2ME3Elektronika/25-26_AudioScope/Material/Fun Generation UA-202.png

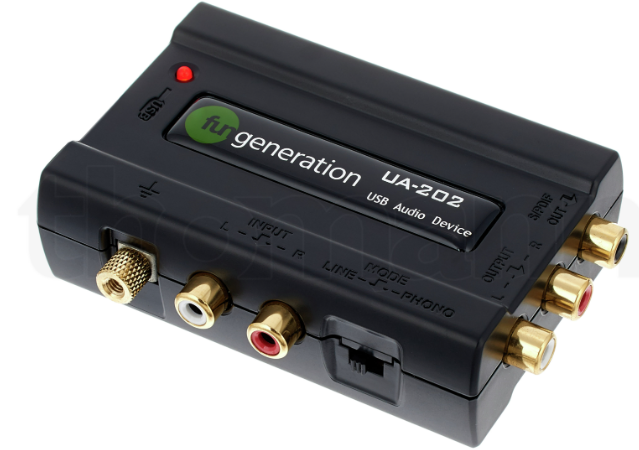
Material/Fun Generation UA-202.png
