2ME3Elektronika/25-26_AudioScope/Material/Raspberry pi 4 model B.png

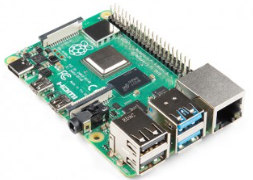
Material/Raspberry pi 4 model B.png
