2ME3Elektronika/25-26_AudioScope/Schematics/Material for PCB/470 Ω Resistance.png

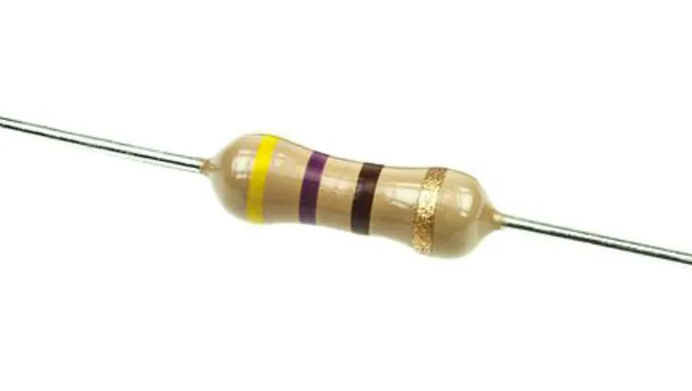
Schematics/Material for PCB/470 Ω Resistance.png
