2ME3Elektronika/25-26_AudioScope/Schematics/Material for PCB/Fixed Terminal Blocks 2P 5.08mm 90DEG.png

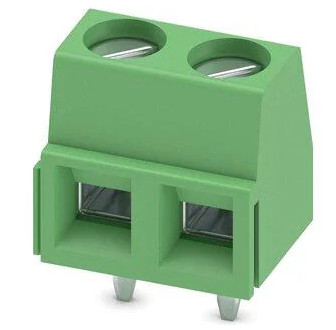
Schematics/Material for PCB/Fixed Terminal Blocks 2P 5.08mm 90DEG.png
