2ME3Elektronika/25-26_AudioScope/Schematics/Material for PCB/Fixed Terminal Blocks 3P 3.5mm 90DEG.png

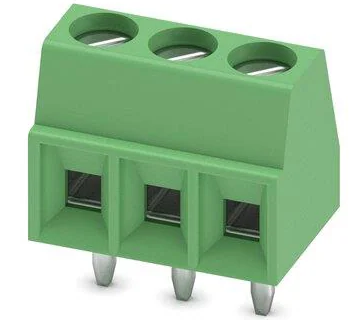
Schematics/Material for PCB/Fixed Terminal Blocks 3P 3.5mm 90DEG.png
