2ME3Elektronika/25-26_AudioScope/Schematics/Material for PCB/Fuseholder.png

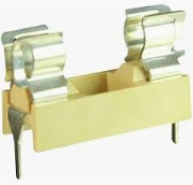
Schematics/Material for PCB/Fuseholder.png
