2ME3Elektronika/25-26_AudioScope/Schematics/Material for PCB/Male 4 pin conector.png

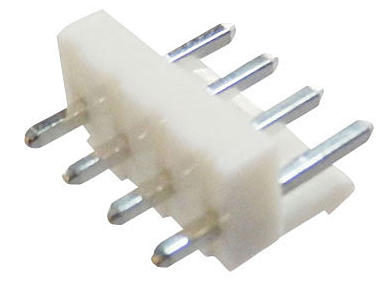
Schematics/Material for PCB/Male 4 pin conector.png
