2ME3Elektronika/25-26_AudioScope/Schematics/Material for PCB/MCP1826S 33EAB Regulator.png

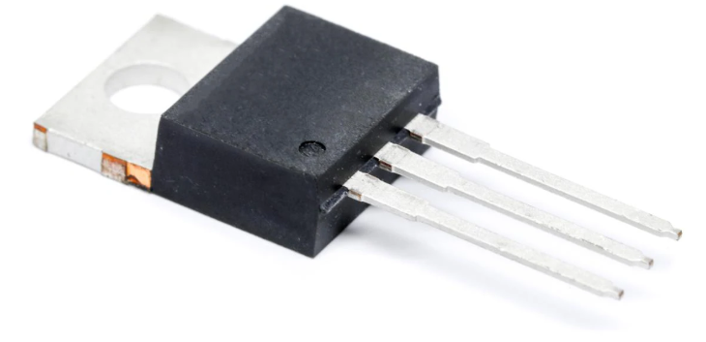
Schematics/Material for PCB/MCP1826S 33EAB Regulator.png
